bkarl/minimal-watch/software/rtc.c

#include "rtc.h"
#include "nfc.h"
#include "interrupt.h"

RTC_HandleTypeDef hrtc;

void rtc_init(void)
{
  hrtc.Instance = RTC;
  hrtc.Init.HourFormat = RTC_HOURFORMAT_24;
  hrtc.Init.AsynchPrediv = 127;
  hrtc.Init.SynchPrediv = 255;
  hrtc.Init.OutPut = RTC_OUTPUT_DISABLE;
  hrtc.Init.OutPutRemap = RTC_OUTPUT_REMAP_NONE;
  hrtc.Init.OutPutPolarity = RTC_OUTPUT_POLARITY_HIGH;
  hrtc.Init.OutPutType = RTC_OUTPUT_TYPE_OPENDRAIN;
  HAL_RTC_Init(&hrtc);
}

void rtc_reset_time() {
  RTC_TimeTypeDef sTime = {0};
  RTC_DateTypeDef sDate = {0};

  sTime.Hours = 23;
  sTime.Minutes = 54;
  sTime.Seconds = 40;
  sTime.DayLightSaving = RTC_DAYLIGHTSAVING_NONE;
  sTime.StoreOperation = RTC_STOREOPERATION_RESET;
  HAL_RTC_SetTime(&hrtc, &sTime, RTC_FORMAT_BIN);
  sDate.WeekDay = RTC_WEEKDAY_MONDAY;
  sDate.Month = RTC_MONTH_JANUARY;
  sDate.Date = 0x1;
  sDate.Year = 0x0;

  HAL_RTC_SetDate(&hrtc, &sDate, RTC_FORMAT_BIN);
}

void rtc_set_time_from_nfc() {
  RTC_TimeTypeDef sTime = {0};
  RTC_DateTypeDef sDate = {0};

  if (!nfc_read_timestamp_record(&sTime, &sDate))
    return;

  sTime.DayLightSaving = RTC_DAYLIGHTSAVING_NONE;
  sTime.StoreOperation = RTC_STOREOPERATION_RESET;
  HAL_RTC_SetTime(&hrtc, &sTime, RTC_FORMAT_BIN);
  HAL_RTC_SetDate(&hrtc, &sDate, RTC_FORMAT_BIN);
  nfc_clear_ndef_message();
}

void rtc_set_alarm() {
  RTC_AlarmTypeDef sAlarm = {0};
	sAlarm.AlarmTime.Hours = 23;
	sAlarm.AlarmTime.Minutes = 59;
	sAlarm.AlarmTime.Seconds = 55;
	sAlarm.AlarmTime.SubSeconds = 0;
	sAlarm.AlarmTime.DayLightSaving = RTC_DAYLIGHTSAVING_NONE;
	sAlarm.AlarmTime.StoreOperation = RTC_STOREOPERATION_RESET;
	sAlarm.AlarmMask = RTC_ALARMMASK_DATEWEEKDAY;
	sAlarm.AlarmSubSecondMask = RTC_ALARMSUBSECONDMASK_ALL;
	sAlarm.AlarmDateWeekDaySel = RTC_ALARMDATEWEEKDAYSEL_DATE;
	sAlarm.AlarmDateWeekDay = 1;
	sAlarm.Alarm = RTC_ALARM_A;

	HAL_RTC_SetAlarm_IT(&hrtc, &sAlarm, RTC_FORMAT_BIN);
  HAL_NVIC_SetPriority(RTC_IRQn, 0, 0);
  HAL_NVIC_EnableIRQ(RTC_IRQn);
}

void rtc_enable_second_tick() {
  RTC_AlarmTypeDef sAlarm = {0};
	sAlarm.AlarmTime.StoreOperation = RTC_STOREOPERATION_RESET;
	sAlarm.AlarmMask = RTC_ALARMMASK_DATEWEEKDAY;
	sAlarm.AlarmSubSecondMask = RTC_ALARMSUBSECONDMASK_ALL;
  sAlarm.Alarm = RTC_ALARM_B;
  sAlarm.AlarmMask = RTC_ALARMMASK_ALL;
	HAL_RTC_SetAlarm_IT(&hrtc, &sAlarm, RTC_FORMAT_BIN);

  HAL_NVIC_SetPriority(RTC_IRQn, 0, 0);
  HAL_NVIC_EnableIRQ(RTC_IRQn);
}

void HAL_RTC_AlarmAEventCallback(RTC_HandleTypeDef *hrtc) {
  UNUSED(hrtc);
  wakeup_reason = WAKEUP_REASON_ALARM;
}

void rtc_disable_second_tick() {
  HAL_RTC_DeactivateAlarm(&hrtc, RTC_ALARM_B);
}
